ltebs-polimi/AY2122_II_Project-2/Documents/bonyu.png

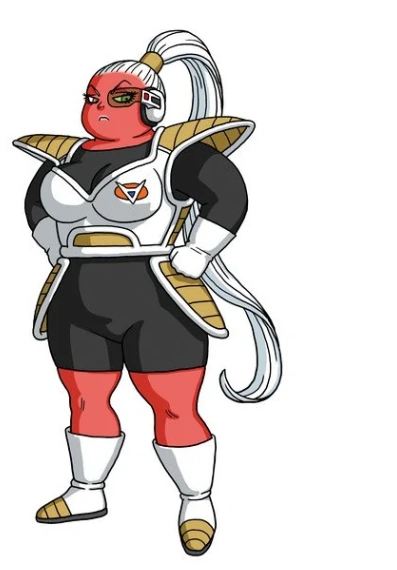
Documents/bonyu.png
