ltebs-polimi/AY2122_II_Project-2/Documents/Gui actiavtion.png

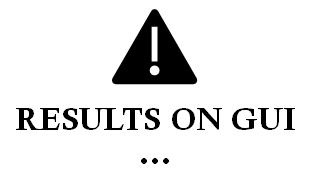
Documents/Gui actiavtion.png
