ltebs-polimi/AY2122_II_Project-2/Documents/gui activation 2.png

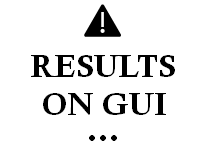
Documents/gui activation 2.png
