ltebs-polimi/AY2122_II_Project-2/PCB/pcb-2.png

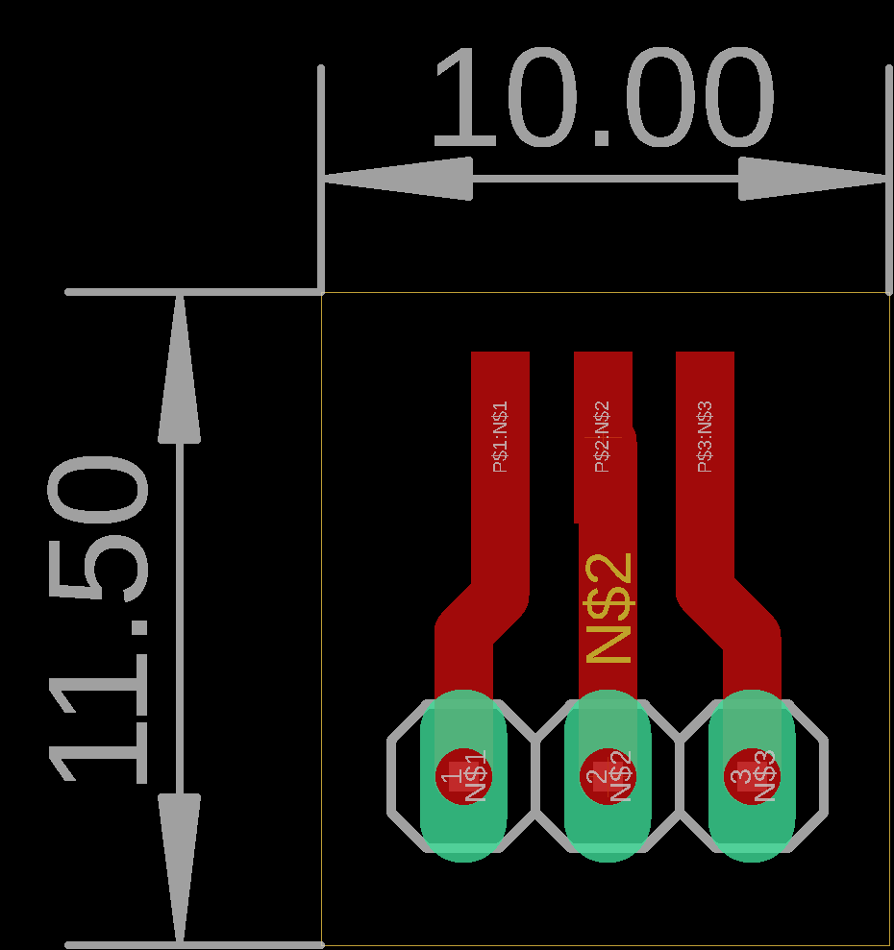
PCB/pcb-2.png
