ltebs-polimi/AY2122_II_Project-2/Presentations/Immagini/ca-80-new.PNG

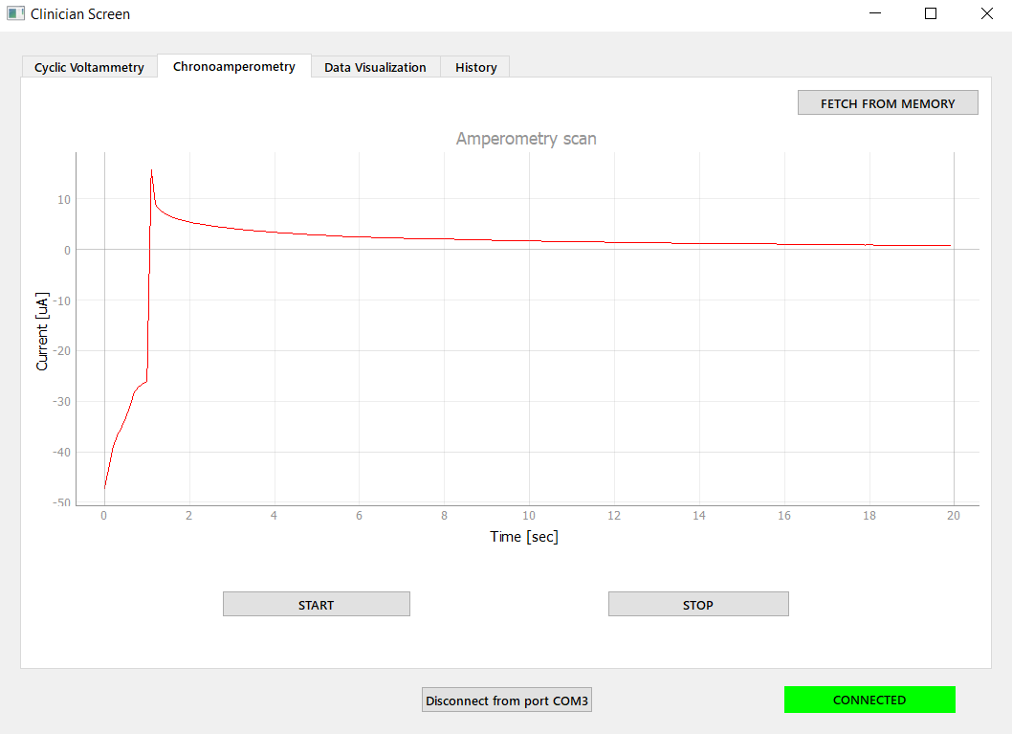
Presentations/Immagini/ca-80-new.PNG
