ltebs-polimi/AY2122_II_Project-2/Presentations/Immagini/CA_80.PNG

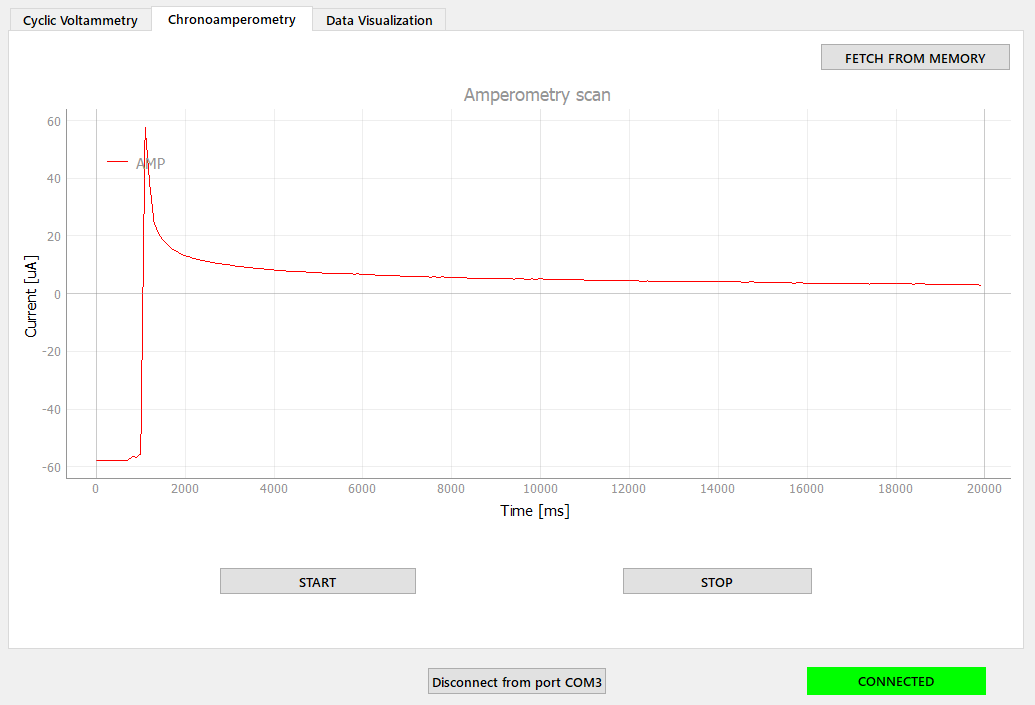
Presentations/Immagini/CA_80.PNG
