ltebs-polimi/AY2122_II_Project-2/Presentations/Immagini/clinician_screen_connessione.PNG

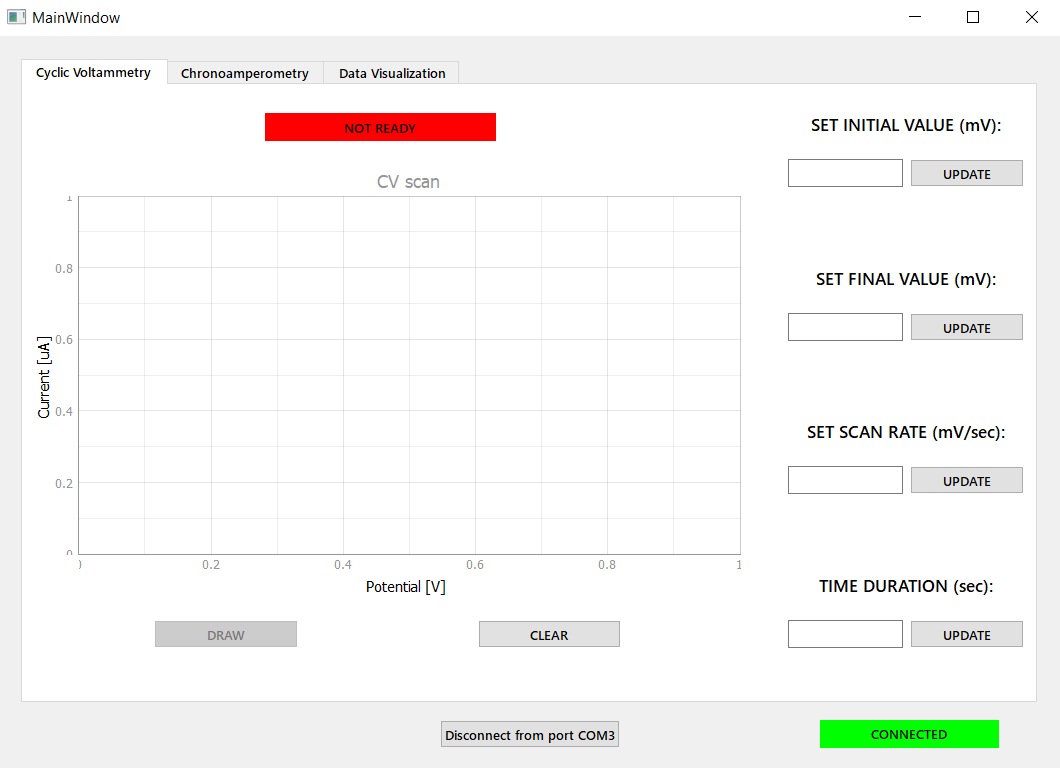
Presentations/Immagini/clinician_screen_connessione.PNG
