ltebs-polimi/AY2122_II_Project-2/Presentations/Immagini/clinician_screen_plot.PNG

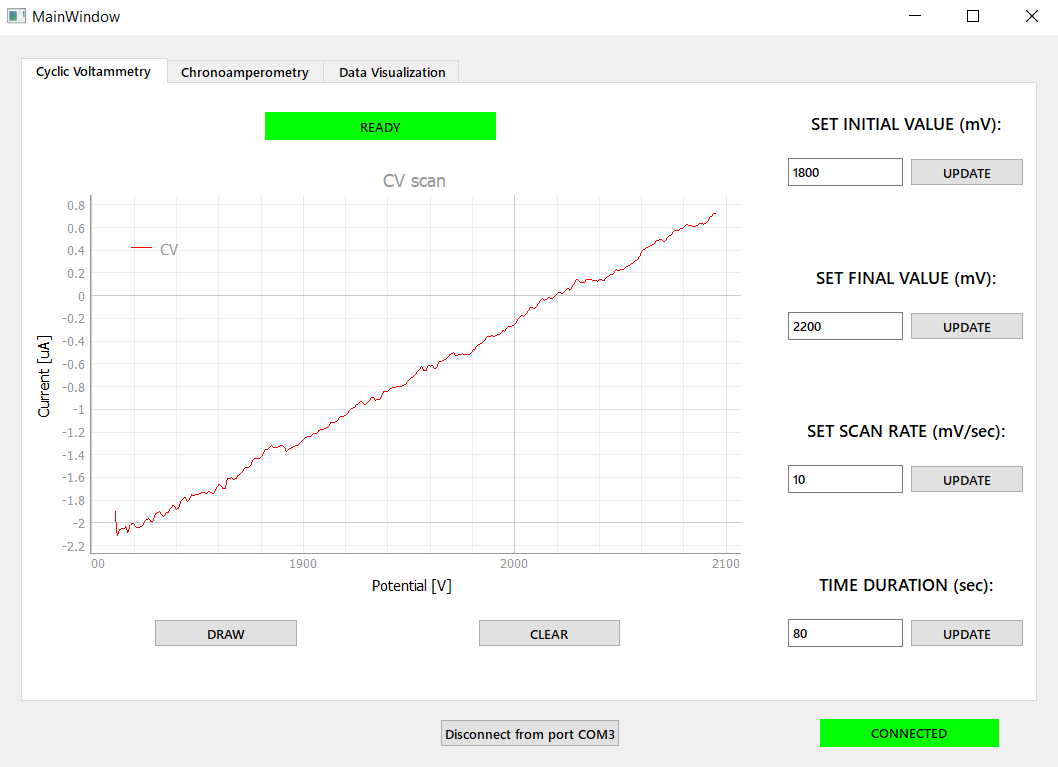
Presentations/Immagini/clinician_screen_plot.PNG
