ltebs-polimi/AY2122_II_Project-2/Presentations/Immagini/cv-80-new.PNG

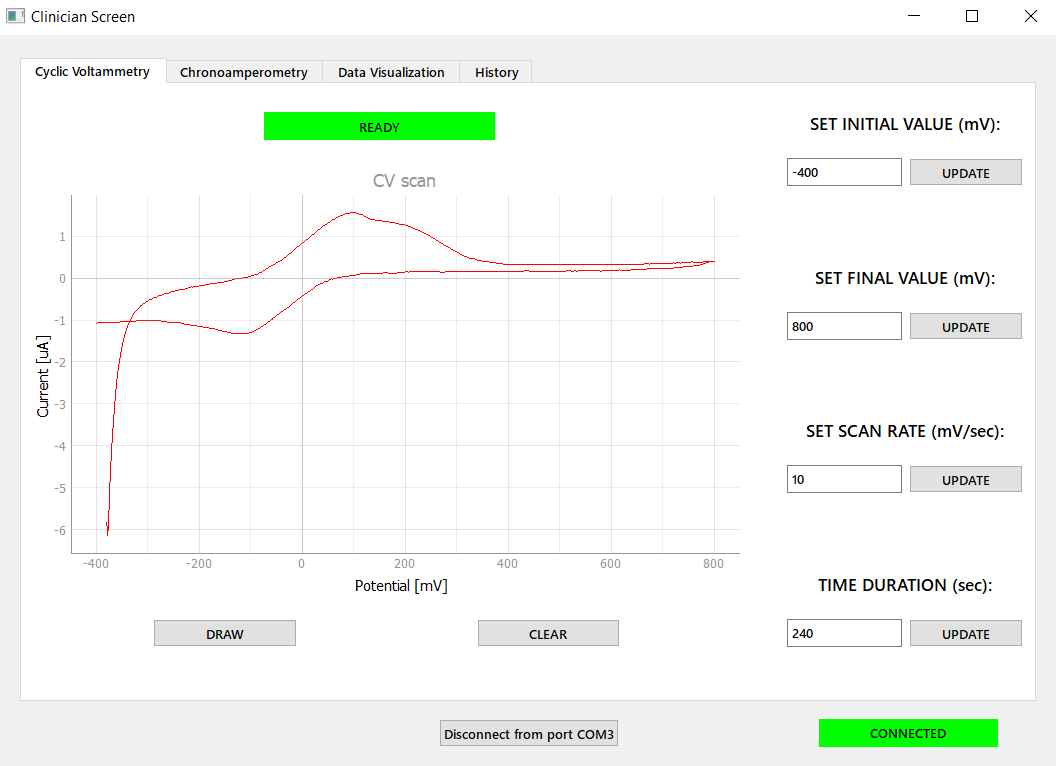
Presentations/Immagini/cv-80-new.PNG
