ltebs-polimi/AY2122_II_Project-2/Presentations/Immagini/grafico CV prese.PNG

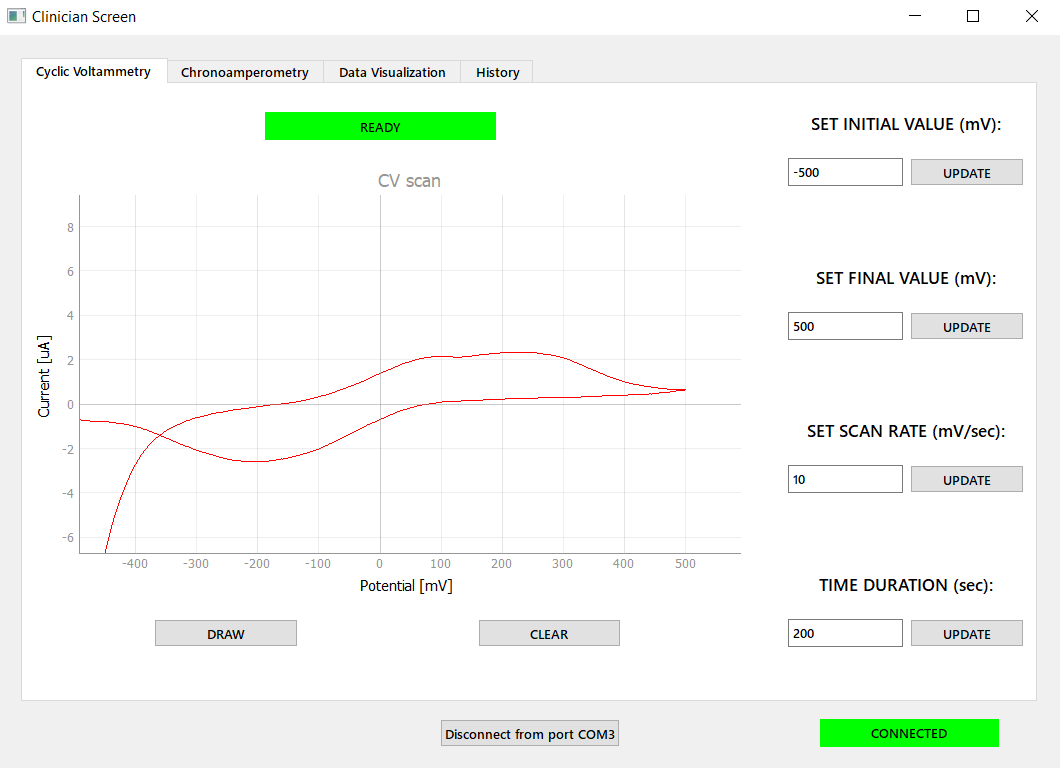
Presentations/Immagini/grafico CV prese.PNG
