ltebs-polimi/AY2122_II_Project-2/Presentations/Immagini/user_screen.PNG

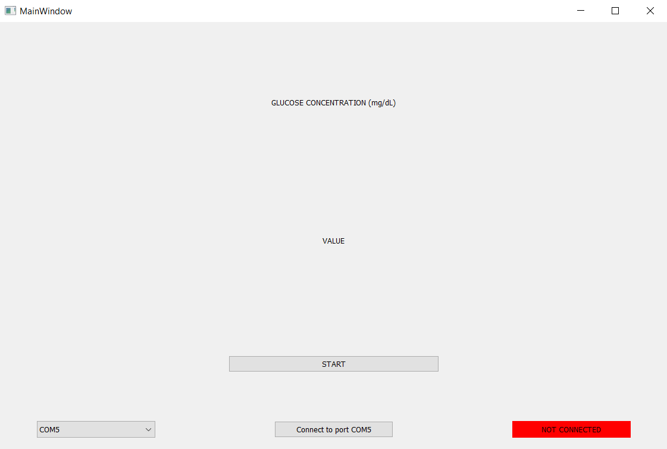
Presentations/Immagini/user_screen.PNG
