ltebs-polimi/AY2122_II_Project-2/Presentations/Immagini/WhatsApp Image 2022-06-21 at 13.48.38.jpeg

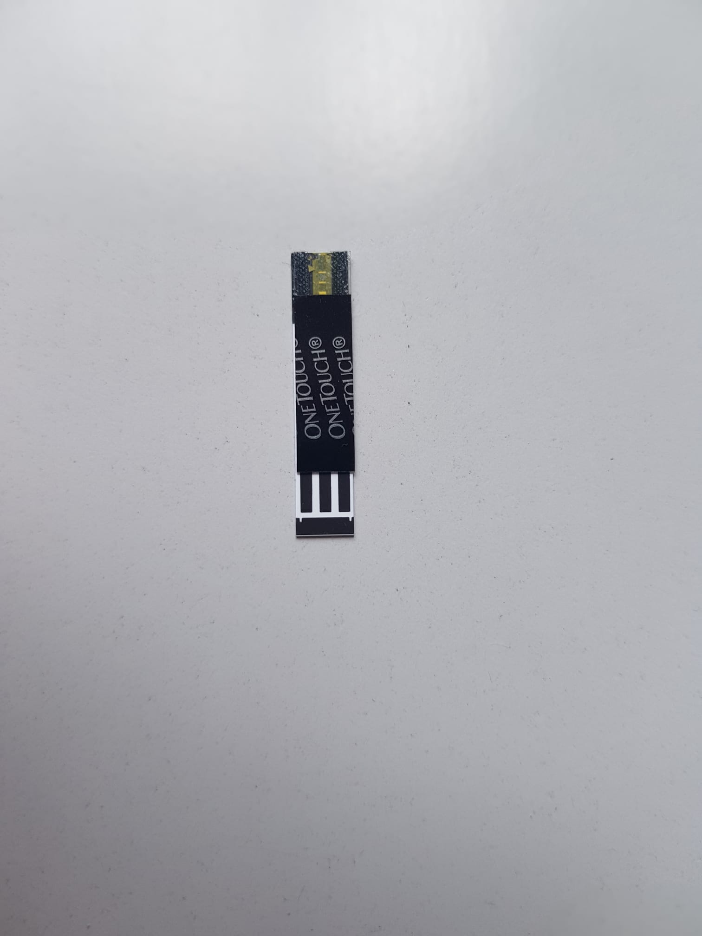
Presentations/Immagini/WhatsApp Image 2022-06-21 at 13.48.38.jpeg
