ltebs-polimi/AY2122_II_Project-2/Presentations/Immagini/WhatsApp Image 2022-06-29 at 13.23.30.jpeg

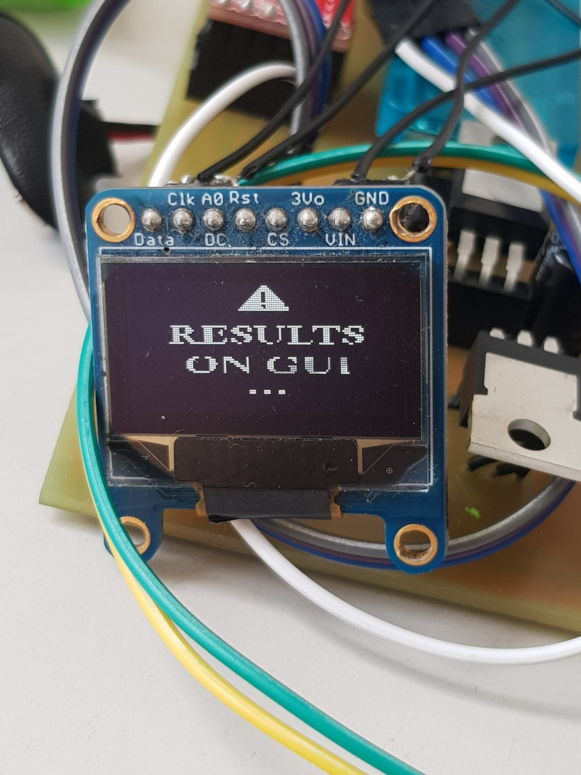
Presentations/Immagini/WhatsApp Image 2022-06-29 at 13.23.30.jpeg
