ltebs-polimi/AY2122_II_Project-2/Regression/Cali_1.png

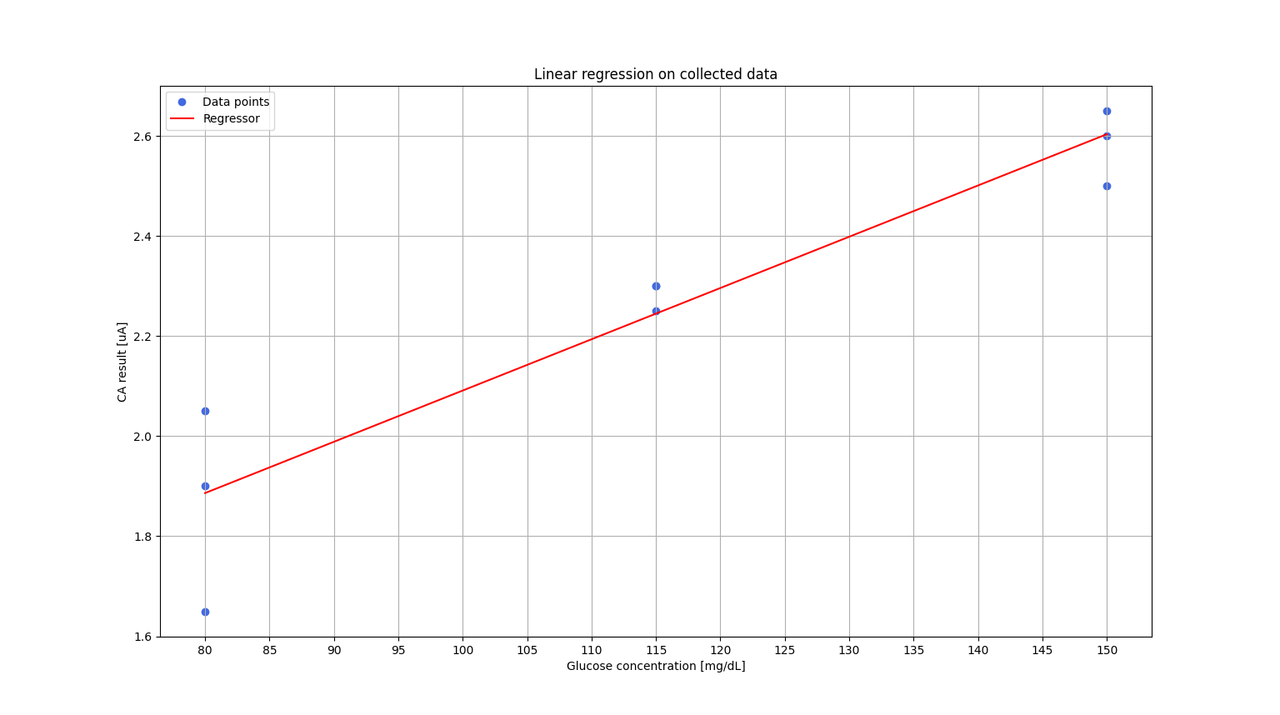
Regression/Cali_1.png
