ltebs-polimi/AY2122_II_Project-2/Regression/Cali_2.png

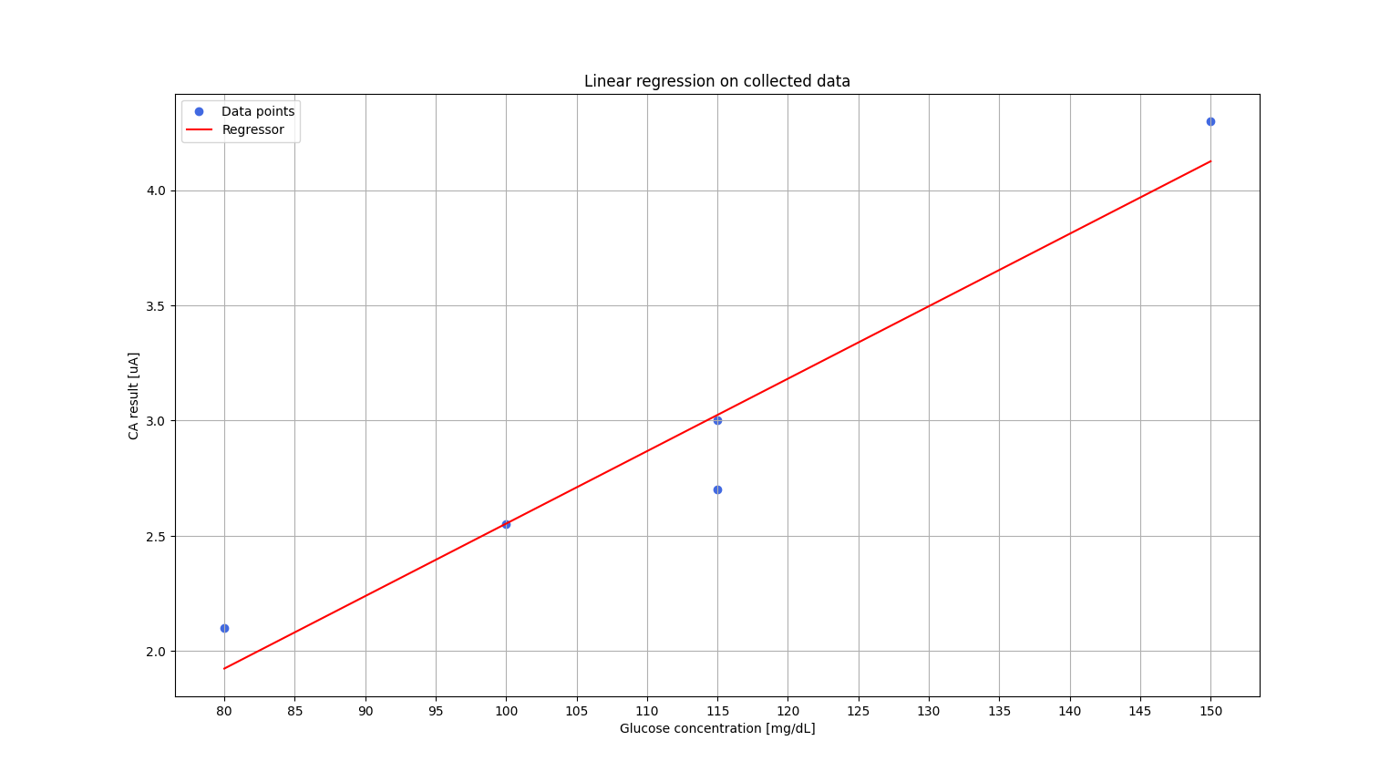
Regression/Cali_2.png
