ltebs-polimi/AY2122_II_Project-2/Regression/Cali_3.png

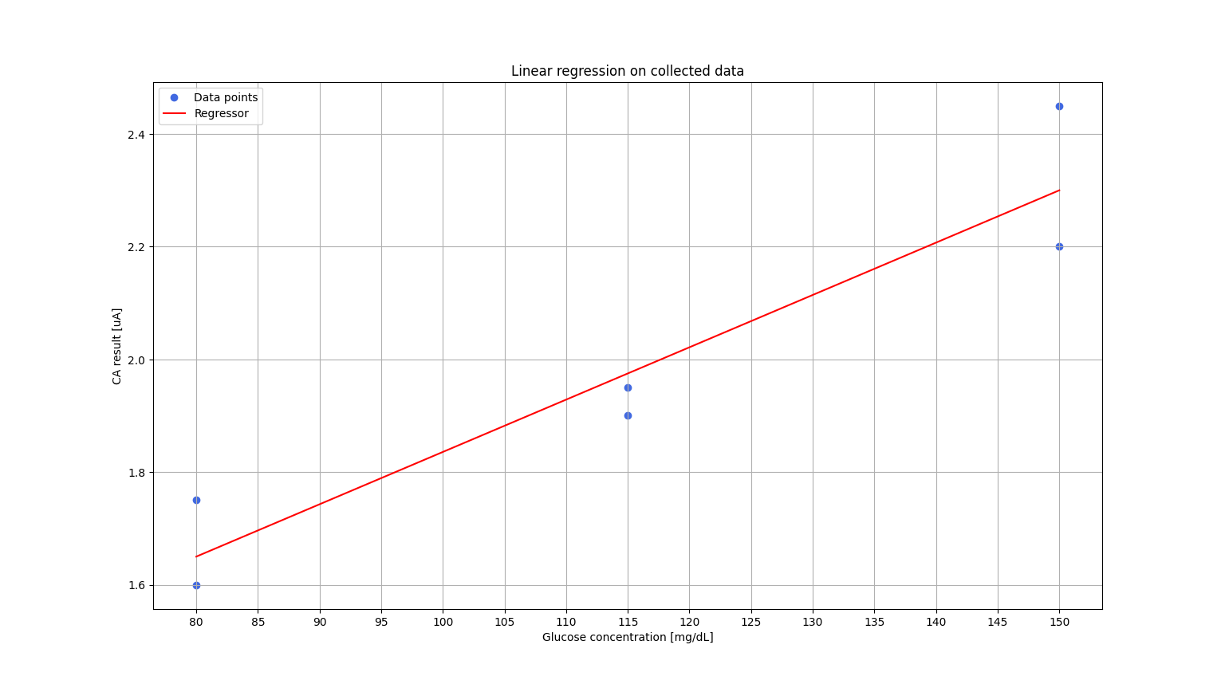
Regression/Cali_3.png
