ltebs-polimi/AY2122_II_Project-2/Presentations/Immagini/history.PNG

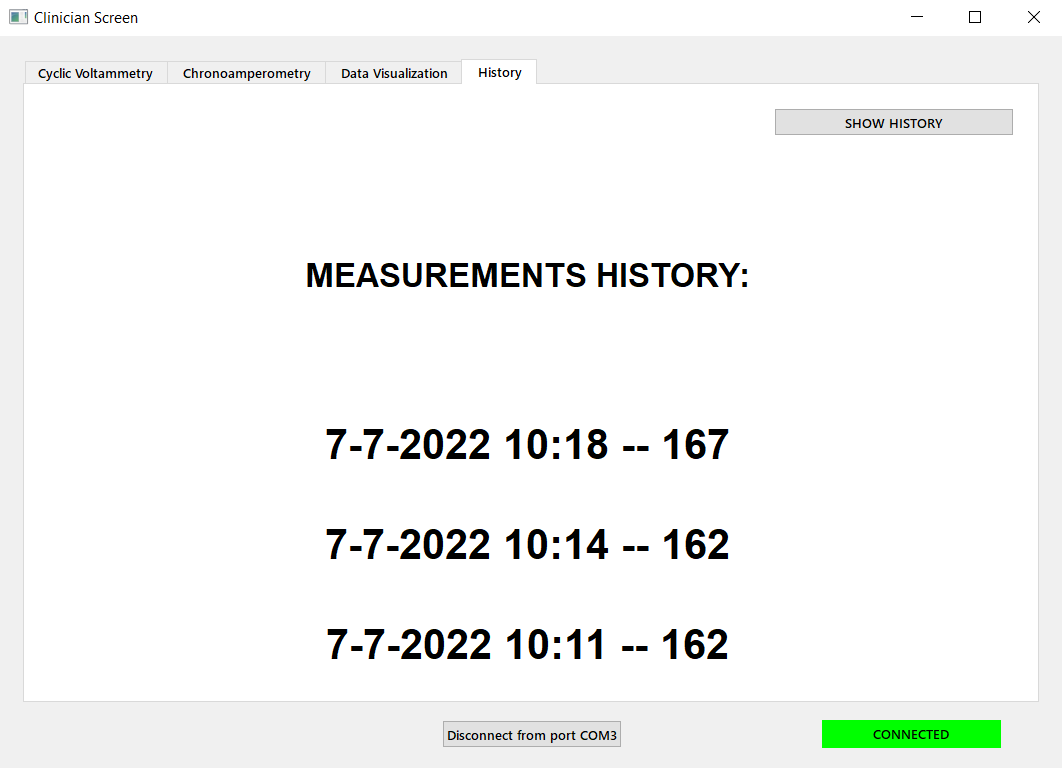
Presentations/Immagini/history.PNG
