ltebs-polimi/AY2122_II_Project-2/Project_design.cydsn/ErrorCodes.h

/* ========================================================================
 *
 * ELECTRONIC TECHNOLOGIES AND BIOSENSORS LABORATORY
 * Academic year 2021/22, II Semester
 * Final Project
 *
 * Authors: Group 2
 *
 * ------------------------- ErrorCodes (header) --------------------------
 * This file contains several definition of error codes to be used 
 * throughout the project to be consisted with the written firmware.
 * ------------------------------------------------------------------------
 * 
 * ========================================================================
*/

#ifndef __ERRORCODES_H
    #define __ERRORCODES_H
    
    typedef enum {
        NO_ERROR,           ///< No error generated
        ERROR               ///< Error generated
    } ErrorCode;

#endif
/* [] END OF FILE */
