ltebs-polimi/AY2122_II_Project-2/Project_design.cydsn/user_selections.h

/* ========================================================================
 *
 * ELECTRONIC TECHNOLOGIES AND BIOSENSORS LABORATORY
 * Academic year 2021/22, II Semester
 * Final Project
 *
 * Authors: Group 2
 *
 * ---------------------- USER SELECTIONS (header) ------------------------
 * Functions related to the user selections from the GUI
 * ------------------------------------------------------------------------
 * 
 * ========================================================================
*/
#ifndef _USER_SELECTIONS_H
    #define _USER_SELECTIONS_H
        
    #include <project.h>
    #include "Globals.h"
    #include "Helper_functions.h"

    /*
    #include "lut_protocols.h"
    #include "usb_protocols.h"
        */
        
        
    #define DO_NOT_RESTART_ADC      0

//Function Prototypes  
    void user_setup_TIA_ADC(uint8 data_buffer[]);
    void user_run_cv_experiment(uint8 data_buffer[]);
    void user_voltage_source_funcs(uint8 data_buffer[]);
    void user_start_cv_run(void);
    void user_reset_device(void);
    void user_identify(void);
    void user_set_isr_timer(uint16 scan_rate);
    void user_chrono_lut_maker(int16 potential_max_current);
    uint16 user_lookup_table_maker(void);
    void user_run_amperometry(void);

//Global variables external identifier
    extern uint8 TIA_resistor_value_index;
    extern uint8 ADC_buffer_index;
  
#endif

/* [] END OF FILE */
