ltebs-polimi/AY2122_II_Project-2/PYTHON GUI/first_screen.py

### IMPORT SOME USEFUL LIBRARIES ###

from PyQt5 import QtCore, QtGui, QtWidgets
from clinician_screen import Ui_ClinicianWindow
from user_screen import Ui_UserWindow


### MAIN WINDOW CLASS ###
class Ui_MainWindow(object):

        
    def openWindow_clinician(self):
        """!
        @brief Function to show the clinician screen.
        """
        self.window=QtWidgets.QMainWindow()
        self.ui= Ui_ClinicianWindow()
        self.ui.setupUi(self.window)
        self.window.show()
        MainWindow.hide() 

    def openWindow_user(self):
        """!
        @brief Function to show the user screen.
        """
        self.window=QtWidgets.QMainWindow()
        self.ui= Ui_UserWindow()
        self.ui.setupUi(self.window)
        self.window.show()
        MainWindow.hide() 

    def setupUi(self, MainWindow):
        MainWindow.setObjectName("MainWindow")
        MainWindow.resize(1100, 858)
        sizePolicy = QtWidgets.QSizePolicy(QtWidgets.QSizePolicy.Preferred, QtWidgets.QSizePolicy.Preferred)
        sizePolicy.setHorizontalStretch(0)
        sizePolicy.setVerticalStretch(0)
        sizePolicy.setHeightForWidth(MainWindow.sizePolicy().hasHeightForWidth())
        MainWindow.setSizePolicy(sizePolicy)
        MainWindow.setMaximumSize(QtCore.QSize(16777215, 16777215))
        self.centralwidget = QtWidgets.QWidget(MainWindow)
        self.centralwidget.setObjectName("centralwidget")
        self.gridLayout = QtWidgets.QGridLayout(self.centralwidget)
        self.gridLayout.setObjectName("gridLayout")
        self.frame = QtWidgets.QFrame(self.centralwidget)
        self.frame.setStyleSheet("background-color: qlineargradient(spread:pad, x1:0, y1:0, x2:0, y2:1, stop:0.277487 rgba(9, 66, 254, 255), stop:1 rgba(255, 255, 255, 255));")
        self.frame.setFrameShape(QtWidgets.QFrame.StyledPanel)
        self.frame.setFrameShadow(QtWidgets.QFrame.Raised)
        self.frame.setObjectName("frame")
        self.gridLayout_3 = QtWidgets.QGridLayout(self.frame)
        self.gridLayout_3.setObjectName("gridLayout_3")
        self.gridLayout_2 = QtWidgets.QGridLayout()
        self.gridLayout_2.setSizeConstraint(QtWidgets.QLayout.SetDefaultConstraint)
        self.gridLayout_2.setContentsMargins(200, -1, 200, -1)
        self.gridLayout_2.setObjectName("gridLayout_2")
        self.label = QtWidgets.QLabel(self.frame)
        sizePolicy = QtWidgets.QSizePolicy(QtWidgets.QSizePolicy.Maximum, QtWidgets.QSizePolicy.Maximum)
        sizePolicy.setHorizontalStretch(0)
        sizePolicy.setVerticalStretch(0)
        sizePolicy.setHeightForWidth(self.label.sizePolicy().hasHeightForWidth())
        self.label.setSizePolicy(sizePolicy)
        self.label.setMaximumSize(QtCore.QSize(550, 400))
        self.label.setStyleSheet("background-color:transparent;")
        self.label.setText("")
        self.label.setPixmap(QtGui.QPixmap("cropped-POLIMI-bianco.png"))
        self.label.setScaledContents(True)
        self.label.setObjectName("label")
        self.gridLayout_2.addWidget(self.label, 0, 1, 1, 1)
        self.label_2 = QtWidgets.QLabel(self.frame)
        font = QtGui.QFont()
        font.setFamily("Yu Gothic UI Semibold")
        font.setPointSize(36)
        font.setBold(True)
        font.setWeight(75)
        self.label_2.setFont(font)
        self.label_2.setStyleSheet("background-color:transparent; color:rgb(255, 223, 62); ")
        self.label_2.setScaledContents(True)
        self.label_2.setAlignment(QtCore.Qt.AlignCenter)
        self.label_2.setObjectName("label_2")
        self.gridLayout_2.addWidget(self.label_2, 1, 1, 1, 1)
        spacerItem = QtWidgets.QSpacerItem(40, 20, QtWidgets.QSizePolicy.Expanding, QtWidgets.QSizePolicy.Minimum)
        self.gridLayout_2.addItem(spacerItem, 0, 0, 1, 1)
        self.label_3 = QtWidgets.QLabel(self.frame)
        font = QtGui.QFont()
        font.setFamily("Yu Gothic UI Semibold")
        font.setPointSize(20)
        font.setBold(True)
        font.setWeight(75)
        self.label_3.setFont(font)
        self.label_3.setStyleSheet("background-color:transparent; color:rgb(255, 255, 255);")
        self.label_3.setScaledContents(True)
        self.label_3.setAlignment(QtCore.Qt.AlignCenter)
        self.label_3.setObjectName("label_3")
        self.gridLayout_2.addWidget(self.label_3, 2, 1, 1, 1)
        self.horizontalLayout = QtWidgets.QHBoxLayout()
        self.horizontalLayout.setSpacing(100)
        self.horizontalLayout.setObjectName("horizontalLayout")
        self.pushButton = QtWidgets.QPushButton(self.frame, clicked= lambda: self.openWindow_clinician())
        sizePolicy = QtWidgets.QSizePolicy(QtWidgets.QSizePolicy.Minimum, QtWidgets.QSizePolicy.Maximum)
        sizePolicy.setHorizontalStretch(0)
        sizePolicy.setVerticalStretch(0)
        sizePolicy.setHeightForWidth(self.pushButton.sizePolicy().hasHeightForWidth())
        self.pushButton.setSizePolicy(sizePolicy)
        self.pushButton.setMaximumSize(QtCore.QSize(16777215, 40))
        font = QtGui.QFont()
        font.setFamily("Yu Gothic UI Semibold")
        font.setPointSize(12)
        font.setBold(True)
        font.setWeight(75)
        self.pushButton.setFont(font)
        self.pushButton.setStyleSheet("background-color: rgb(255, 223, 62); border-radius:20px; color:rgba(9, 66, 254, 255);")
        self.pushButton.setObjectName("pushButton")
        self.horizontalLayout.addWidget(self.pushButton)
        self.pushButton_2 = QtWidgets.QPushButton(self.frame, clicked= lambda: self.openWindow_user())
        sizePolicy = QtWidgets.QSizePolicy(QtWidgets.QSizePolicy.Minimum, QtWidgets.QSizePolicy.Maximum)
        sizePolicy.setHorizontalStretch(0)
        sizePolicy.setVerticalStretch(0)
        sizePolicy.setHeightForWidth(self.pushButton_2.sizePolicy().hasHeightForWidth())
        self.pushButton_2.setSizePolicy(sizePolicy)
        self.pushButton_2.setMaximumSize(QtCore.QSize(16777215, 40))
        font = QtGui.QFont()
        font.setFamily("Yu Gothic UI Semibold")
        font.setPointSize(12)
        font.setBold(True)
        font.setWeight(75)
        self.pushButton_2.setFont(font)
        self.pushButton_2.setStyleSheet("background-color: rgb(255, 223, 62); border-radius:20px; color:rgba(9, 66, 254, 255);")
        self.pushButton_2.setObjectName("pushButton_2")
        self.horizontalLayout.addWidget(self.pushButton_2)
        self.gridLayout_2.addLayout(self.horizontalLayout, 3, 1, 1, 1)
        spacerItem1 = QtWidgets.QSpacerItem(40, 20, QtWidgets.QSizePolicy.Expanding, QtWidgets.QSizePolicy.Minimum)
        self.gridLayout_2.addItem(spacerItem1, 0, 2, 1, 1)
        self.gridLayout_2.setRowMinimumHeight(1, 150)
        self.gridLayout_2.setRowMinimumHeight(2, 100)
        self.gridLayout_2.setRowMinimumHeight(3, 150)
        self.gridLayout_3.addLayout(self.gridLayout_2, 0, 0, 1, 1)
        self.gridLayout.addWidget(self.frame, 0, 0, 1, 1)
        MainWindow.setCentralWidget(self.centralwidget)

        self.retranslateUi(MainWindow)
        QtCore.QMetaObject.connectSlotsByName(MainWindow)

    def retranslateUi(self, MainWindow):
        _translate = QtCore.QCoreApplication.translate
        MainWindow.setWindowTitle(_translate("MainWindow", "MainWindow"))
        self.label_2.setText(_translate("MainWindow", "GLUCOMETER"))
        self.label_3.setText(_translate("MainWindow", "Are you a clinician or a user?"))
        self.pushButton.setText(_translate("MainWindow", "Clinician"))
        self.pushButton_2.setText(_translate("MainWindow", "User"))

if __name__ == "__main__":
    import sys
    app = QtWidgets.QApplication(sys.argv)
    MainWindow = QtWidgets.QMainWindow()
    ui = Ui_MainWindow()
    ui.setupUi(MainWindow)
    MainWindow.show()
    sys.exit(app.exec_())
